vives-project-xp/MusicLightTiles/img/electrical_diagram_v1.5.png

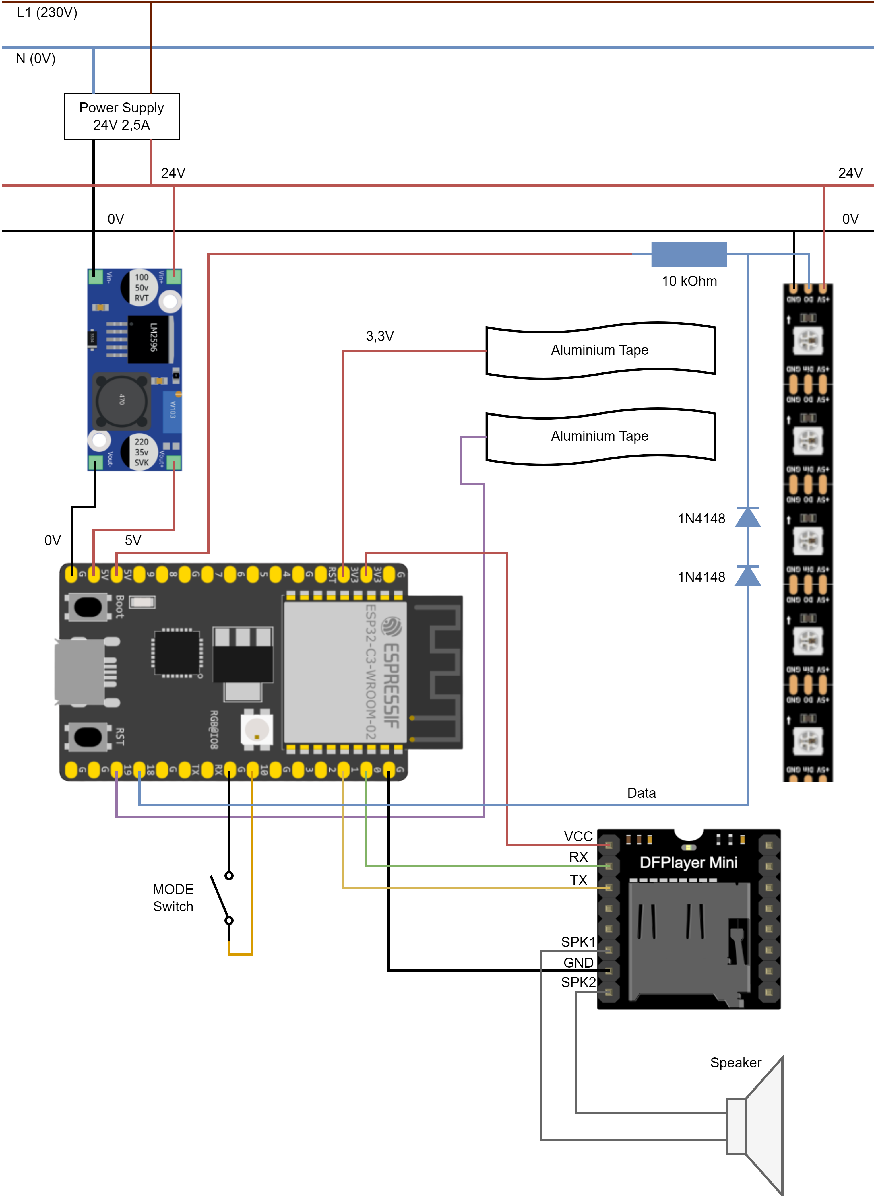
img/electrical_diagram_v1.5.png
